JayShoe/t-dsp_tac5212_pro_audio_module/3d_models/LED_SK6812MINI-E.step

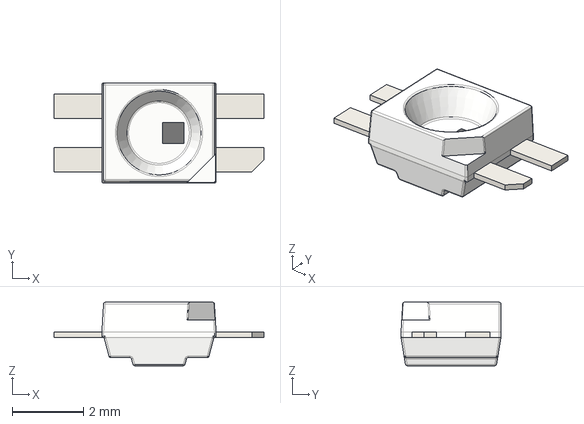
[picture p17: CAD file, 2025-04-21]
3d_models/LED_SK6812MINI-E.step
5.88 x 2.80 x 1.78 mm
