JayShoe/t-dsp_tac5212_pro_audio_module/3d_models/Same_Sky_SJ3-35044A.step

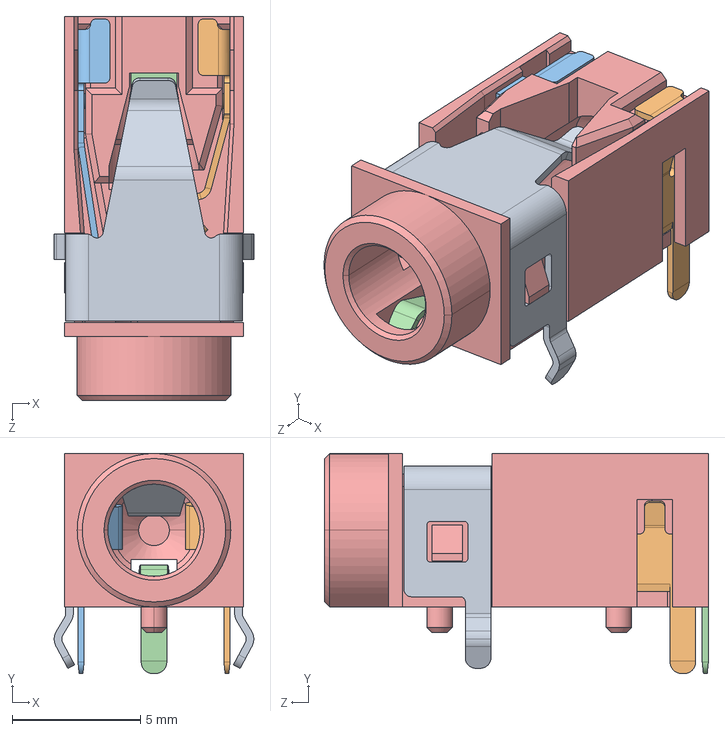
[picture p20: CAD file, 2025-04-21]
3d_models/Same_Sky_SJ3-35044A.step
7.80 x 8.60 x 15.0 mm
