JayShoe/t-dsp_tac5212_pro_audio_module/3d_models/2120--3DModel-STEP-630548.STEP

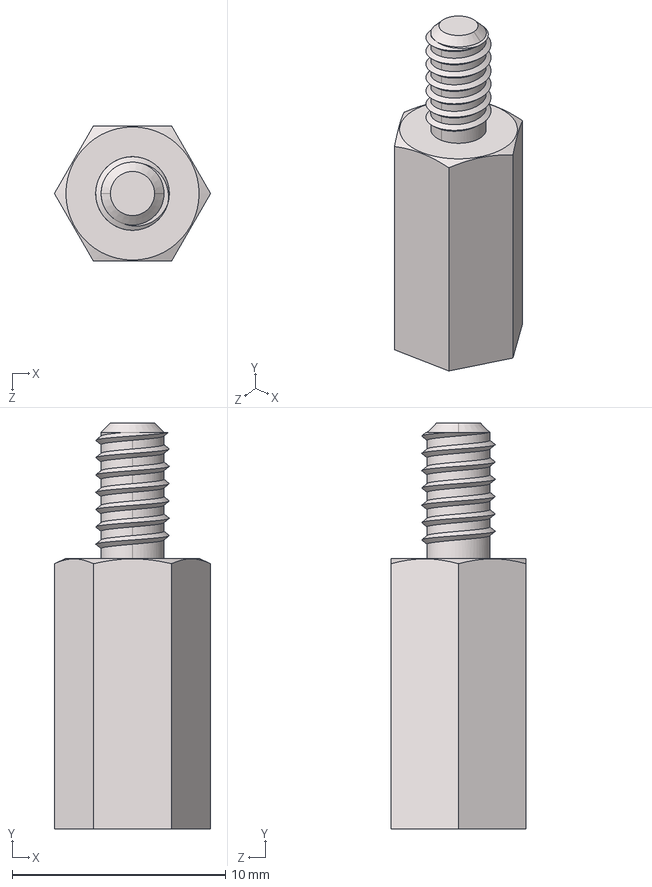
[picture p21: CAD file, 2024-12-20]
3d_models/2120--3DModel-STEP-630548.STEP
7.33 x 19.1 x 6.35 mm
