JayShoe/t-dsp_tac5212_pro_audio_module/3d_models/1808--3DModel-STEP-630548.STEP

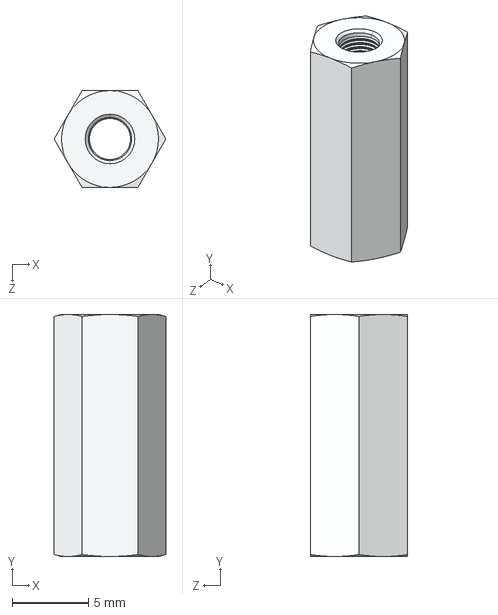
[picture p22: CAD file, 2024-12-20]
3d_models/1808--3DModel-STEP-630548.STEP
7.33 x 15.9 x 6.35 mm
