JayShoe/t-dsp_tac5212_pro_audio_module/3d_models/TE_1775485-1_BATTERY.step

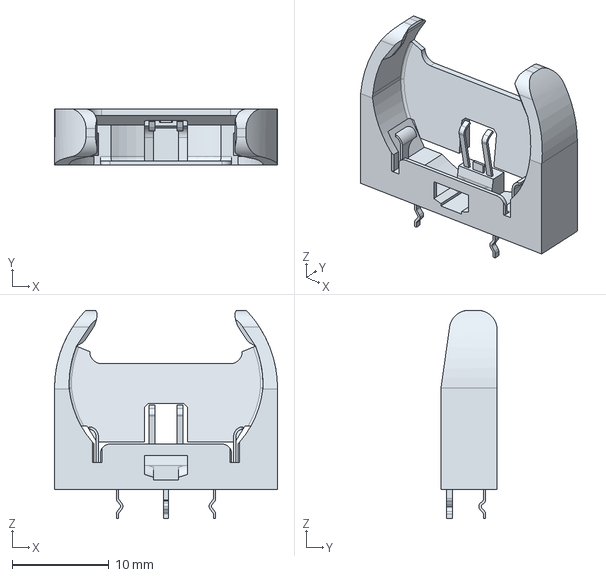
[picture p25: CAD file, 2024-03-24]
3d_models/TE_1775485-1_BATTERY.step
23.0 x 5.80 x 21.5 mm
