JayShoe/t-dsp_tac5212_pro_audio_module/3d_models/d-nc3fah.stp

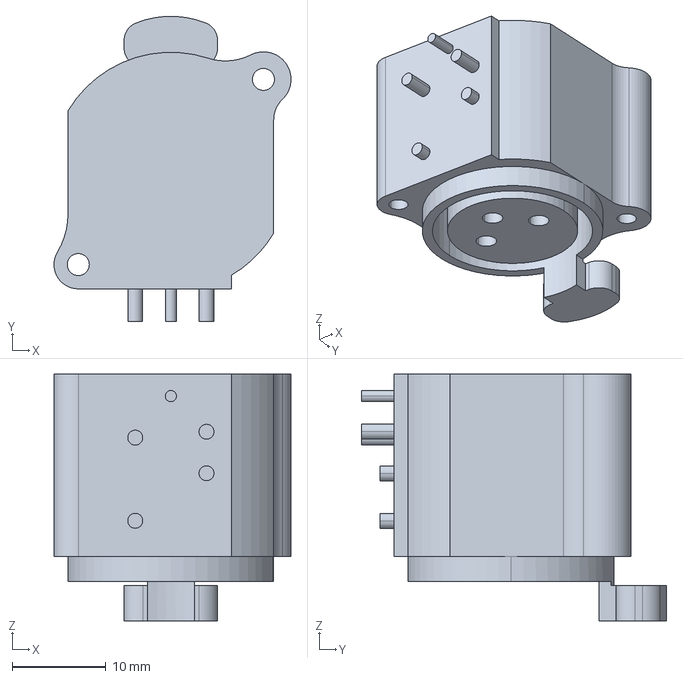
[picture p32: CAD file, 2024-02-26]
3d_models/d-nc3fah.stp
25.3 x 32.6 x 26.4 mm
