JayShoe/t-dsp_tac5212_pro_audio_module/3d_models/DIN-5.STEP

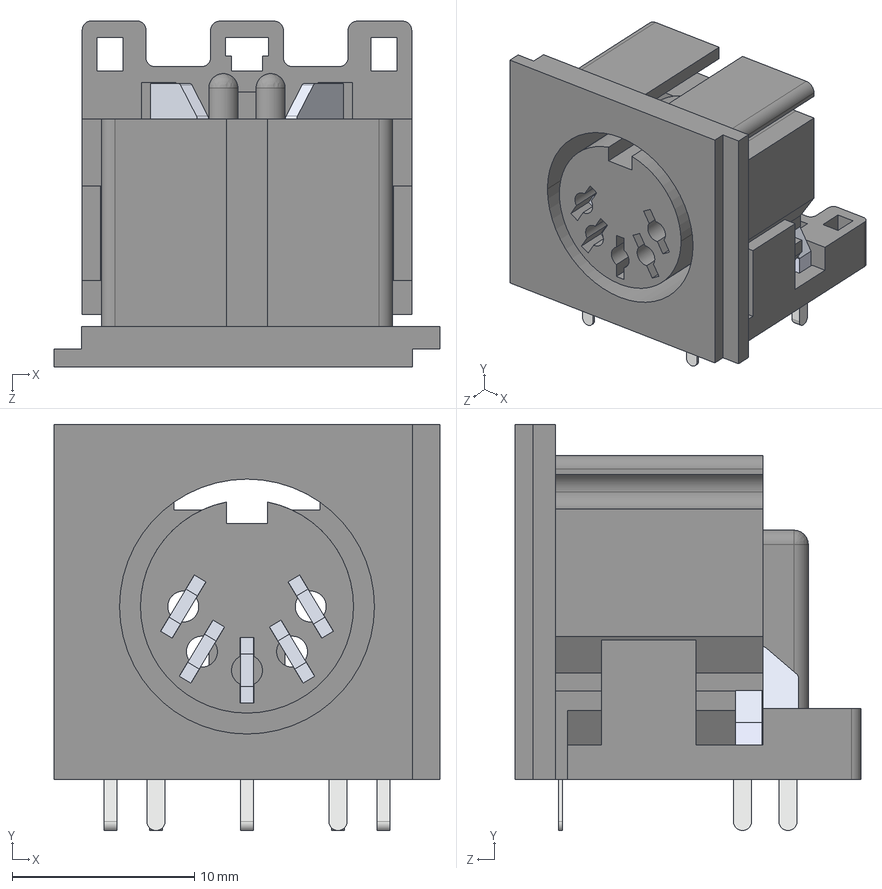
[picture p39: CAD file, 2024-02-26]
3d_models/DIN-5.STEP
21.2 x 22.3 x 19.0 mm
DIN5 A
DIN5 B
DIN5 C
DIN D x 2
DIN E x 2
DIN EE x 2
DIN G
DIN DD x 2
