JayShoe/t-dsp_tac5212_pro_audio_module/3d_models/ncj6fav-1.stp

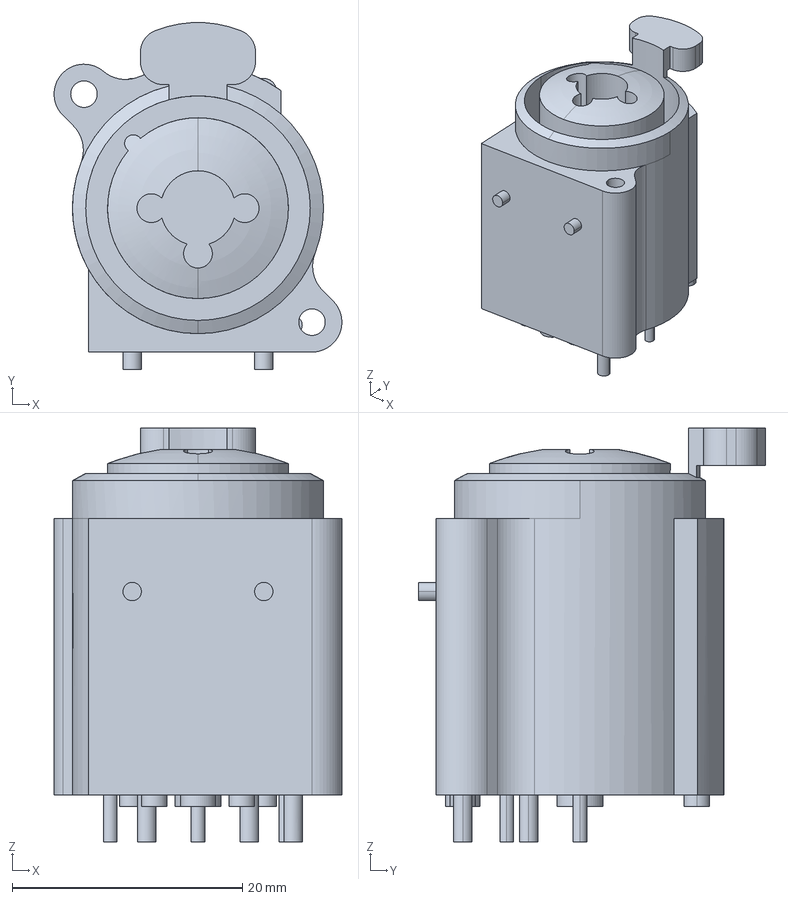
[picture p45: CAD file, 2024-02-26]
3d_models/ncj6fav-1.stp
25.0 x 30.1 x 36.0 mm
