JayShoe/t-dsp_tac5212_pro_audio_module/3d_models/3-D NCJ6FAH.stp

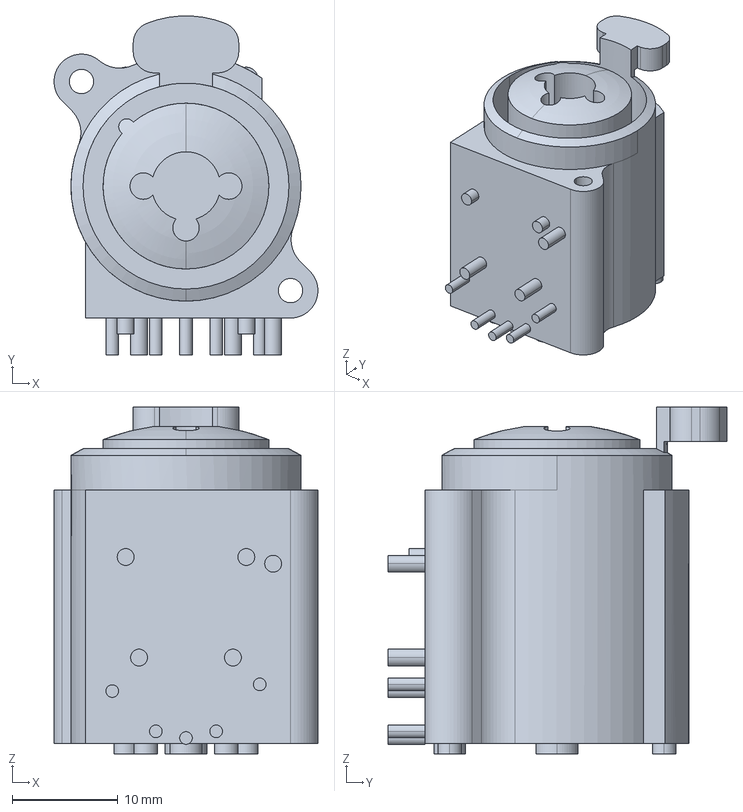
[picture p52: CAD file, 2024-02-26]
3d_models/3-D NCJ6FAH.stp
25.0 x 32.1 x 32.9 mm
