JayShoe/t-dsp_tac5212_pro_audio_module/3d_models/SO-8_5.3x6.2mm_P1.27mm.step

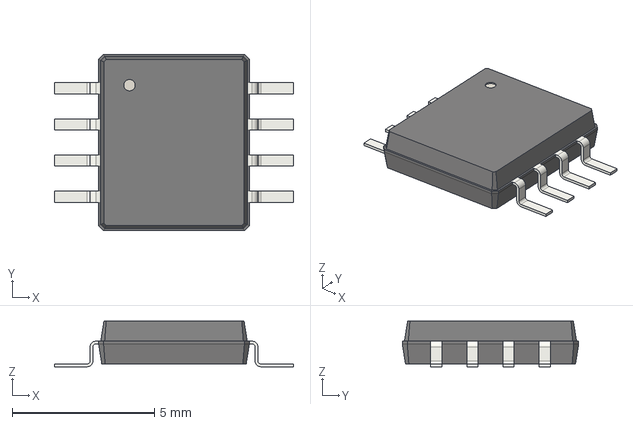
[picture p54: CAD file, 2024-02-26]
3d_models/SO-8_5.3x6.2mm_P1.27mm.step
8.40 x 6.20 x 1.60 mm
