JayShoe/t-dsp_tac5212_pro_audio_module/3d_models/3-d-nmj6hcd3.stp

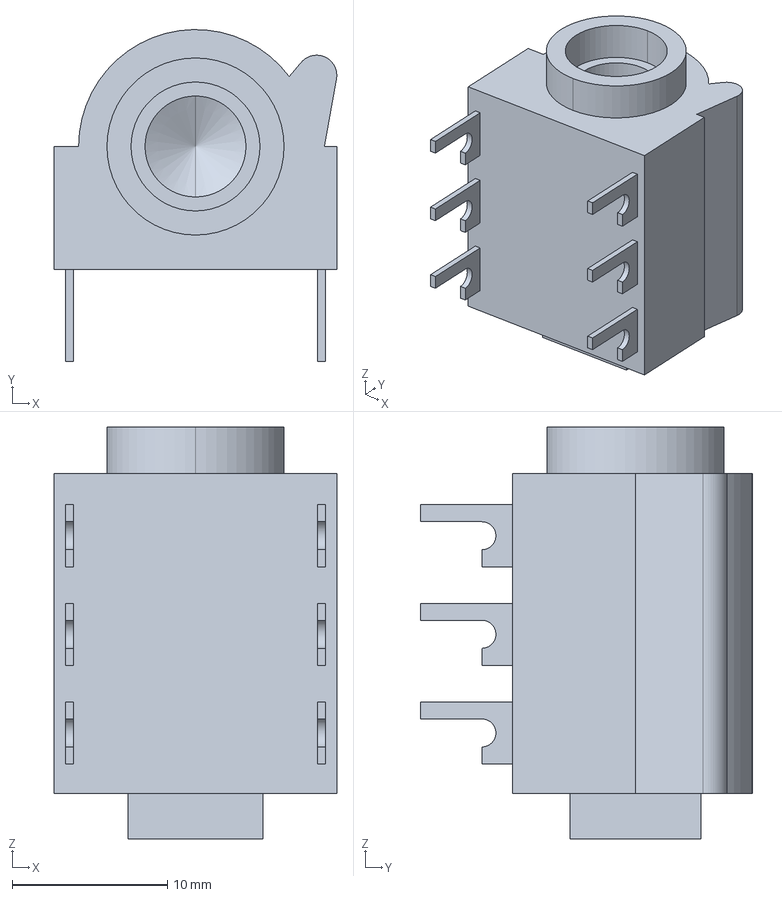
[picture p55: CAD file, 2024-02-26]
3d_models/3-d-nmj6hcd3.stp
18.2 x 21.4 x 26.5 mm
